Jianliang-Shen/Ragtime_Panthera/1_3D_Model/0_Solidworks2022/有d435/gripper/夹爪外壳.SLDPRT

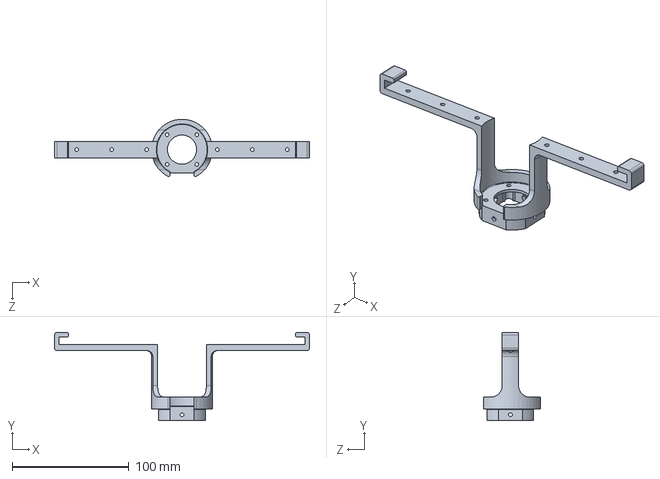
[picture p18: CAD file, 2025-05-28]
1_3D_Model/0_Solidworks2022/有d435/gripper/夹爪外壳.SLDPRT
218.6 x 75.5 x 49.3 mm
