Jianliang-Shen/Ragtime_Panthera/1_3D_Model/0_Solidworks2022/有d435/gripper/平行夹爪stl/外壳内挡块.STL

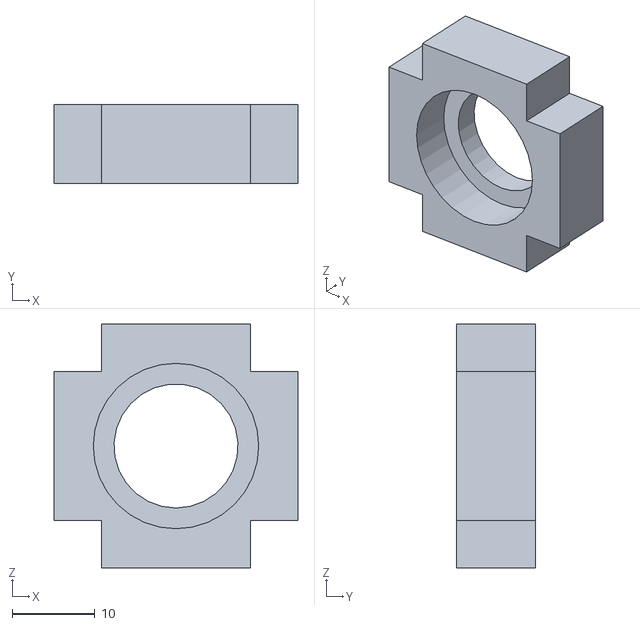
[picture p19: CAD file, 2025-05-28]
1_3D_Model/0_Solidworks2022/有d435/gripper/平行夹爪stl/外壳内挡块.STL
29.5 x 9.50 x 29.5
