Jianliang-Shen/Ragtime_Panthera/1_3D_Model/2_JLC_metalplate/304_stanless_steel/三四轴连杆.STEP

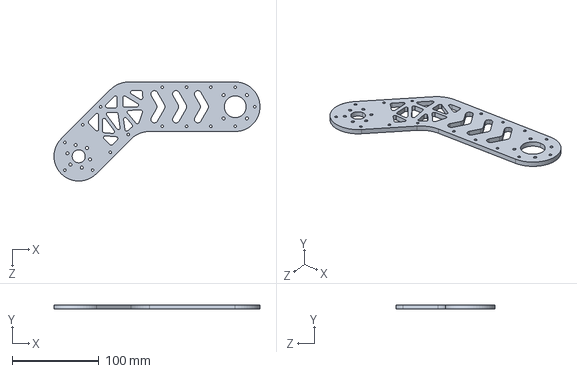
[picture p20: CAD file, 2025-06-30]
1_3D_Model/2_JLC_metalplate/304_stanless_steel/三四轴连杆.STEP
236.9 x 5.00 x 113.9 mm
