Jianliang-Shen/Ragtime_Panthera/1_3D_Model/2_JLC_metalplate/6061_aluminum_alloy/五六轴连接件1.STEP

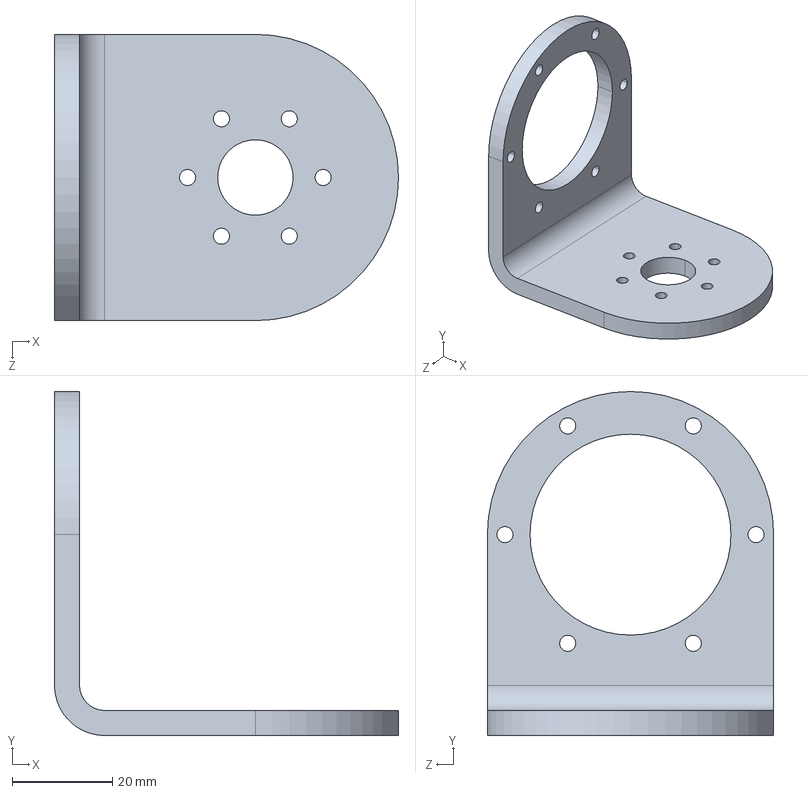
[picture p21: CAD file, 2025-05-02]
1_3D_Model/2_JLC_metalplate/6061_aluminum_alloy/五六轴连接件1.STEP
68.5 x 68.5 x 57.0 mm
