Jianliang-Shen/Ragtime_Panthera/6_Panthera_Robot/assets/link1.STL

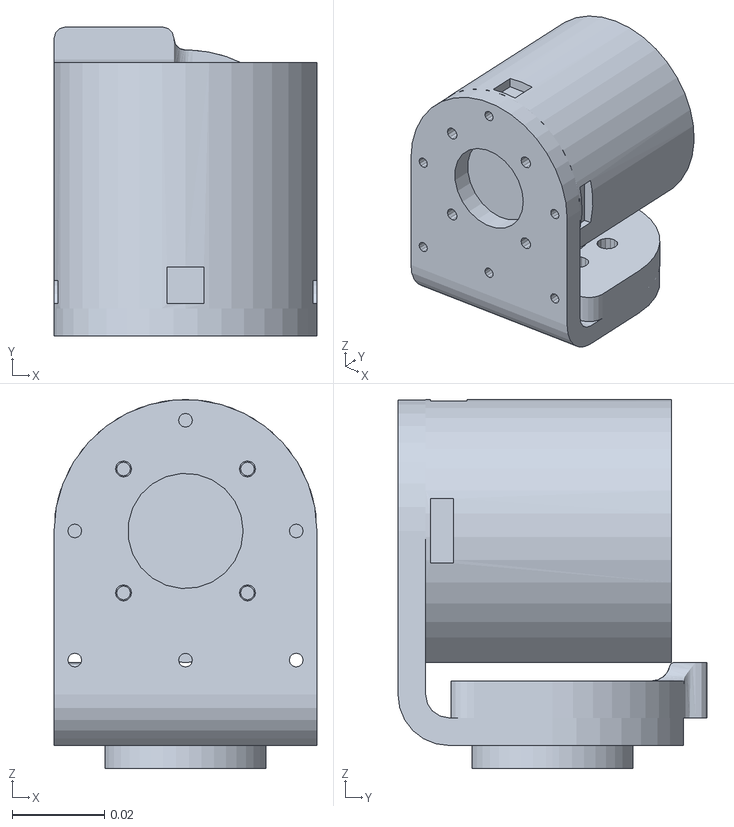
[picture p22: CAD file, 2025-05-02]
6_Panthera_Robot/assets/link1.STL
0.057 x 0.067 x 0.08
