Jianliang-Shen/Ragtime_Panthera/6_Panthera_Robot/assets/table/tabletop.obj

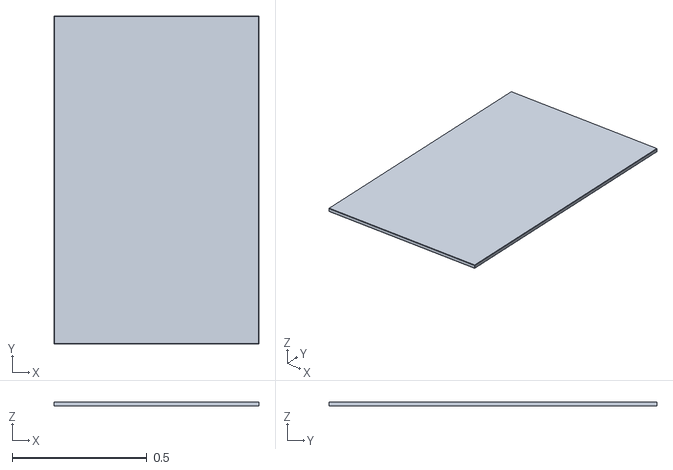
[picture p23: CAD file, 2025-08-23]
6_Panthera_Robot/assets/table/tabletop.obj
0.762 x 1.22 x 0.016
