Jianliang-Shen/Ragtime_Panthera/1_3D_Model/0_Solidworks2022/无d435/arm/四五轴连接件.SLDPRT

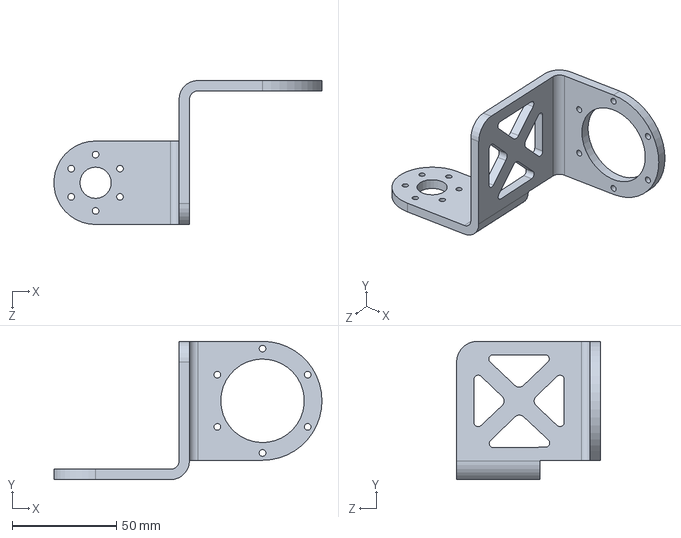
[picture p24: CAD file, 2025-06-30]
1_3D_Model/0_Solidworks2022/无d435/arm/四五轴连接件.SLDPRT
128.4 x 66.3 x 69.0 mm
