Jianliang-Shen/Ragtime_Panthera/1_3D_Model/0_Solidworks2022/无d435/gripper/MGW9导轨滑块模组/MGW9C滑块.SLDPRT

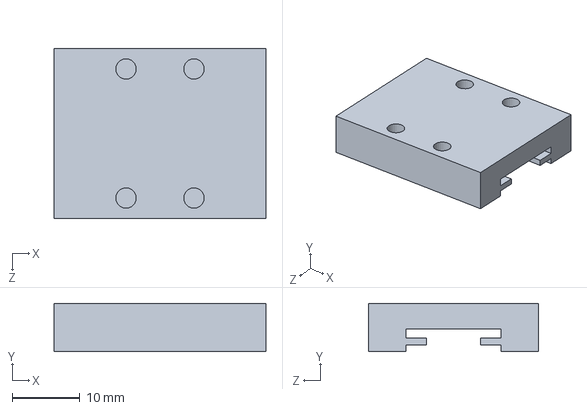
[picture p25: CAD file, 2025-05-02]
1_3D_Model/0_Solidworks2022/无d435/gripper/MGW9导轨滑块模组/MGW9C滑块.SLDPRT
31.2 x 7.10 x 25.0 mm
