Jianliang-Shen/Ragtime_Panthera/1_3D_Model/0_Solidworks2022/无d435/gripper/齿条.SLDPRT

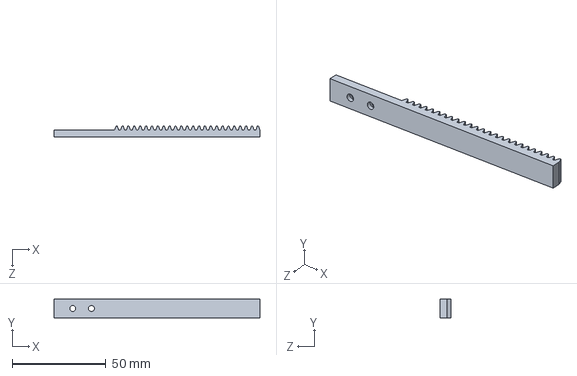
[picture p26: CAD file, 2025-05-28]
1_3D_Model/0_Solidworks2022/无d435/gripper/齿条.SLDPRT
110.0 x 10.0 x 6.00 mm
