Jianliang-Shen/Ragtime_Panthera/1_3D_Model/0_Solidworks2022/有d435/gripper/MGW9导轨滑块模组/MGW9导轨.SLDPRT

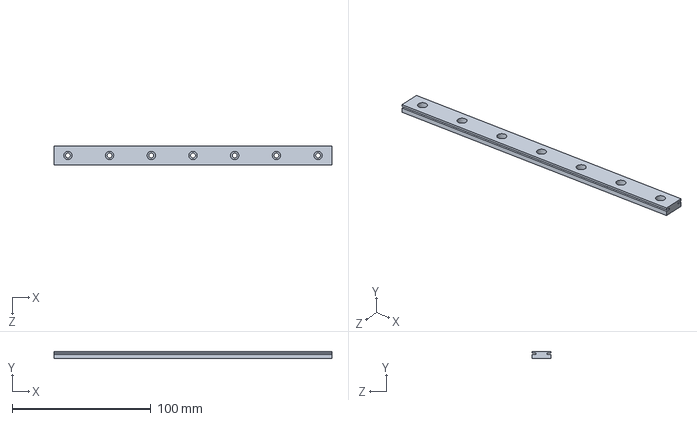
[picture p27: CAD file, 2025-05-02]
1_3D_Model/0_Solidworks2022/有d435/gripper/MGW9导轨滑块模组/MGW9导轨.SLDPRT
200.0 x 5.20 x 14.0 mm
