Jianliang-Shen/Ragtime_Panthera/1_3D_Model/2_JLC_metalplate/304_stanless_steel/二三轴连杆.STEP

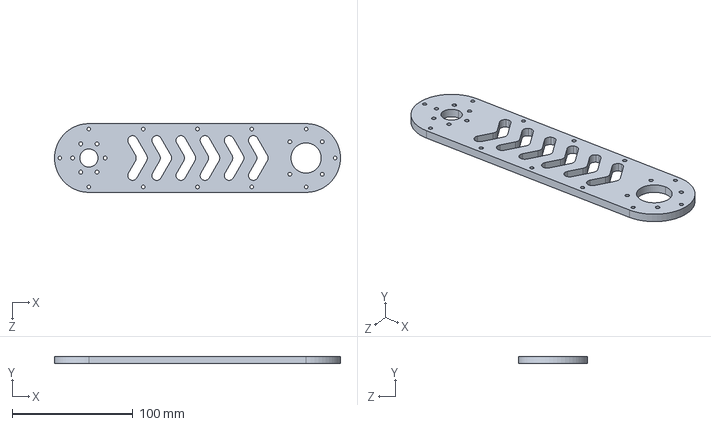
[picture p28: CAD file, 2025-06-30]
1_3D_Model/2_JLC_metalplate/304_stanless_steel/二三轴连杆.STEP
237.0 x 6.00 x 57.0 mm
