Jianliang-Shen/Ragtime_Panthera/6_Panthera_Robot/assets/link6.STL

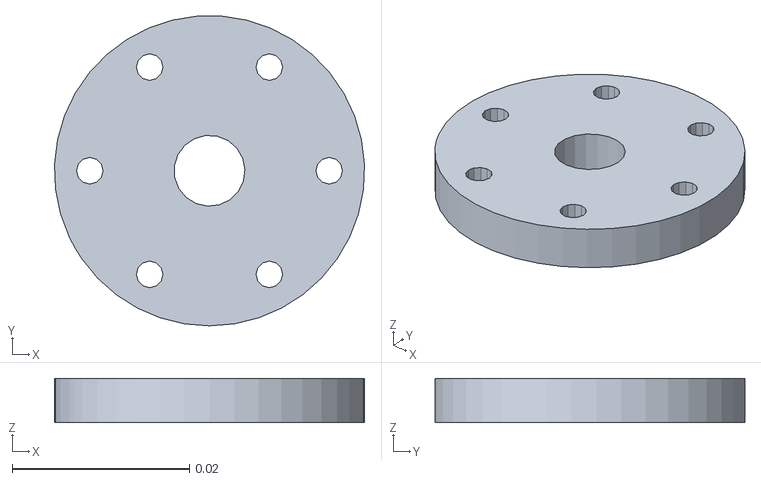
[picture p29: CAD file, 2025-05-02]
6_Panthera_Robot/assets/link6.STL
0.035 x 0.0349 x 0.005
