Jianliang-Shen/Ragtime_Panthera/6_Panthera_Robot/assets/table/tablelegs.obj

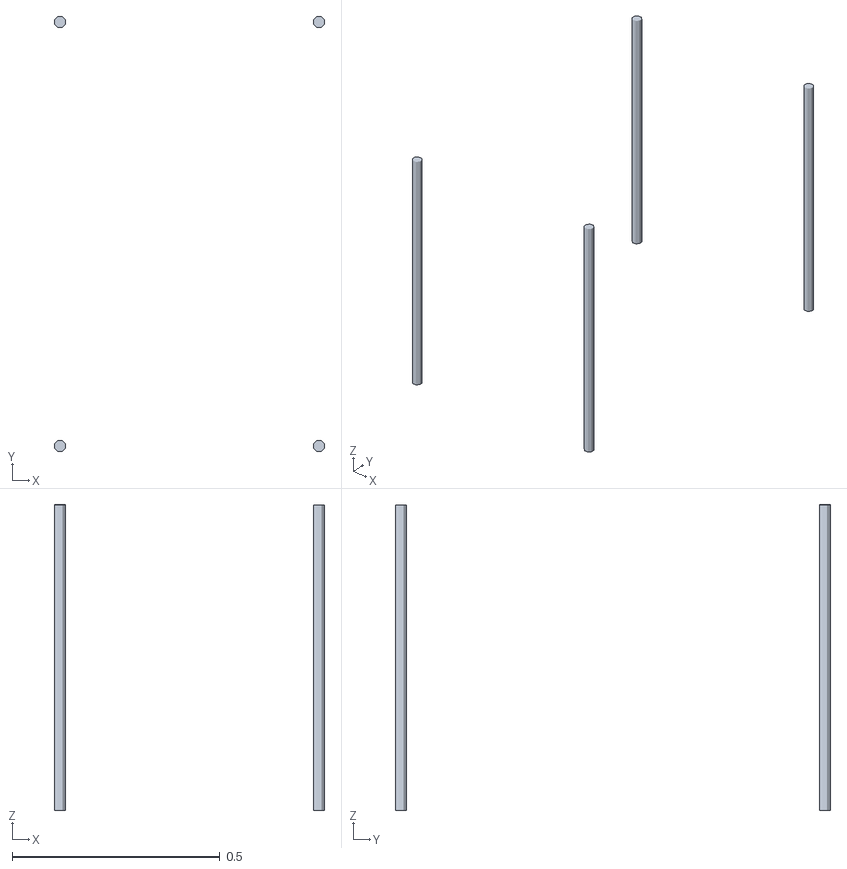
[picture p30: CAD file, 2025-08-23]
6_Panthera_Robot/assets/table/tablelegs.obj
0.65 x 1.05 x 0.737
