Jianliang-Shen/Ragtime_Panthera/1_3D_Model/0_Solidworks2022/无d435/arm/4310电机/4310电机定子.SLDPRT

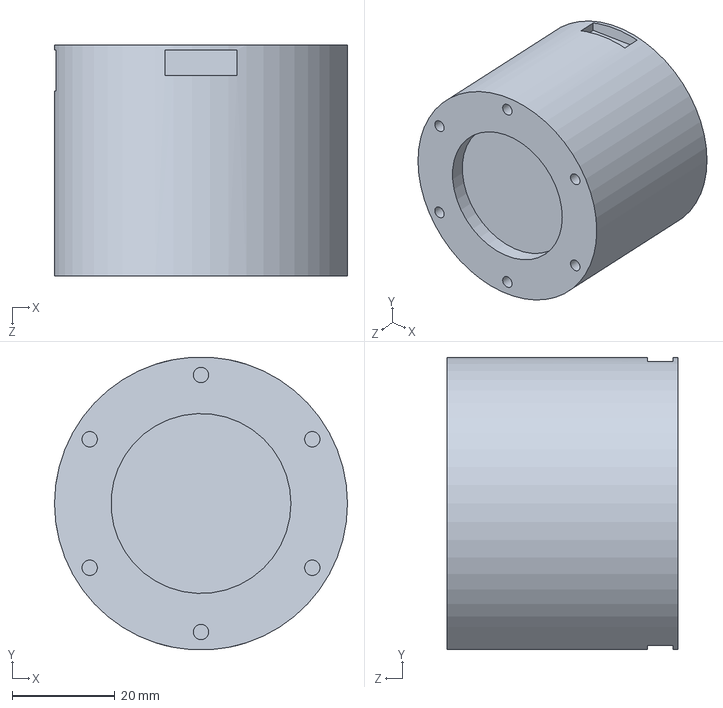
[picture p31: CAD file, 2025-05-02]
1_3D_Model/0_Solidworks2022/无d435/arm/4310电机/4310电机定子.SLDPRT
57.0 x 56.9 x 45.0 mm
