Jianliang-Shen/Ragtime_Panthera/1_3D_Model/0_Solidworks2022/无d435/arm/底板.SLDPRT

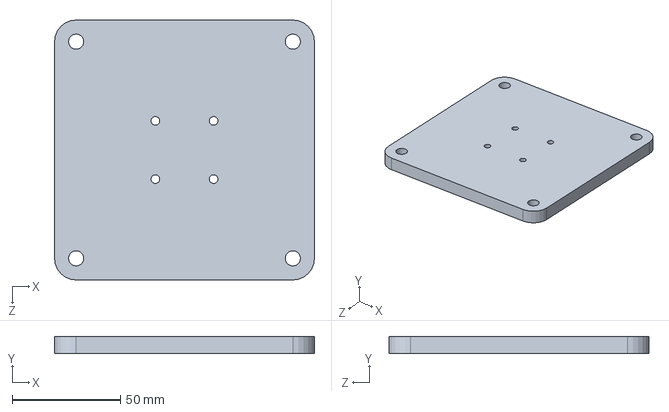
[picture p32: CAD file, 2025-05-28]
1_3D_Model/0_Solidworks2022/无d435/arm/底板.SLDPRT
120.0 x 8.00 x 120.0 mm
