Jianliang-Shen/Ragtime_Panthera/1_3D_Model/0_Solidworks2022/无d435/gripper/达妙3510轮毂电机/3510定子.SLDPRT

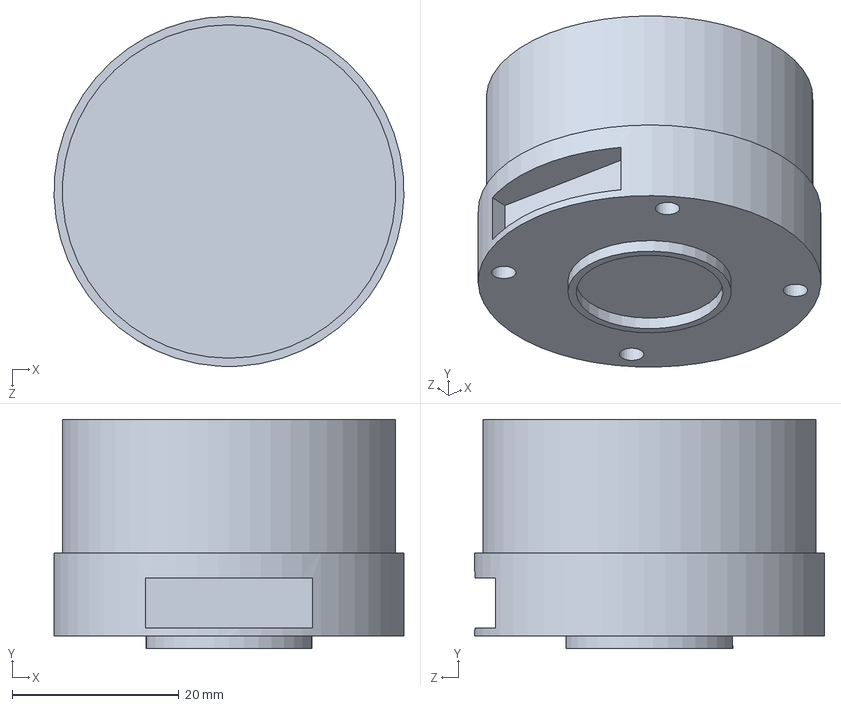
[picture p33: CAD file, 2025-05-02]
1_3D_Model/0_Solidworks2022/无d435/gripper/达妙3510轮毂电机/3510定子.SLDPRT
42.0 x 27.5 x 42.0 mm
