Jianliang-Shen/Ragtime_Panthera/1_3D_Model/2_JLC_metalplate/304_stanless_steel/一二轴连接件.STEP

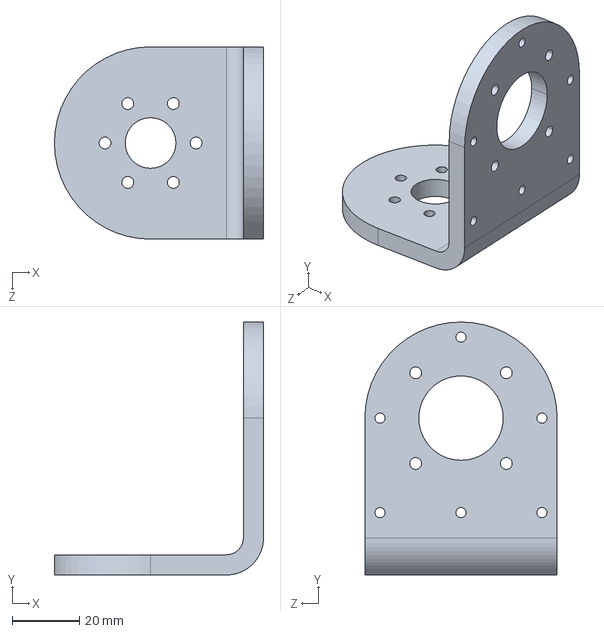
[picture p34: CAD file, 2025-05-02]
1_3D_Model/2_JLC_metalplate/304_stanless_steel/一二轴连接件.STEP
62.0 x 75.0 x 57.0 mm
