Jianliang-Shen/Ragtime_Panthera/6_Panthera_Robot/assets/link4.STL

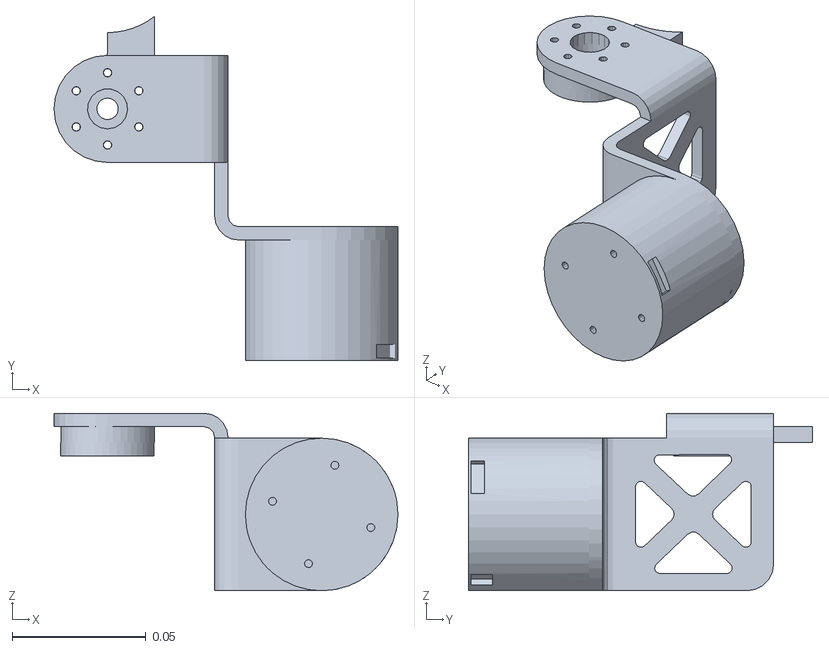
[picture p35: CAD file, 2025-05-02]
6_Panthera_Robot/assets/link4.STL
0.129 x 0.129 x 0.0663
