Jianliang-Shen/Ragtime_Panthera/6_Panthera_Robot/assets/table/Desk.obj

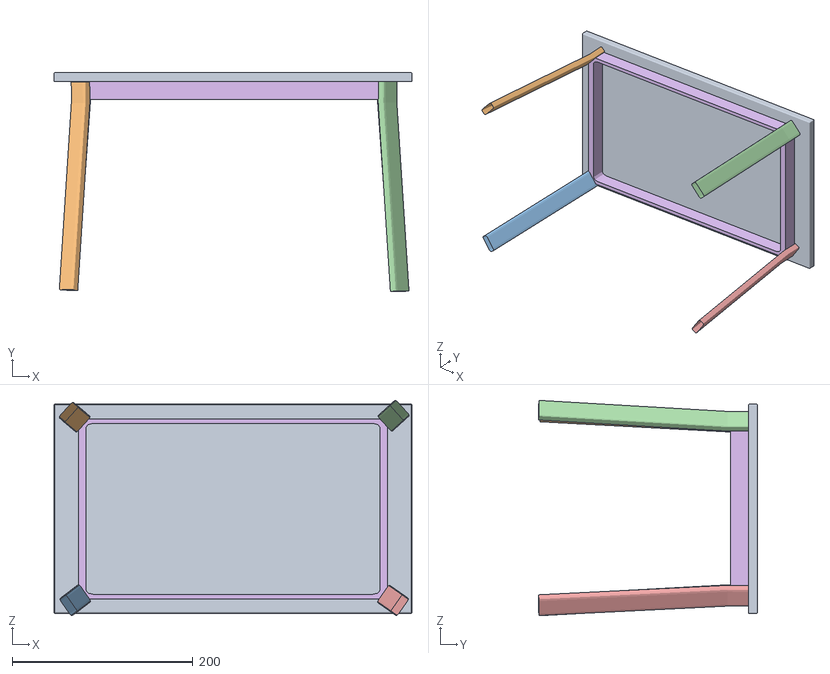
[picture p36: CAD file, 2025-08-23]
6_Panthera_Robot/assets/table/Desk.obj
396.0 x 242.2 x 238.1
Top
Leg:4
Leg:3
Leg:2
Leg:1
Under
