Jianliang-Shen/Ragtime_Panthera/1_3D_Model/0_Solidworks2022/无d435/gripper/转子齿轮连接件.SLDPRT

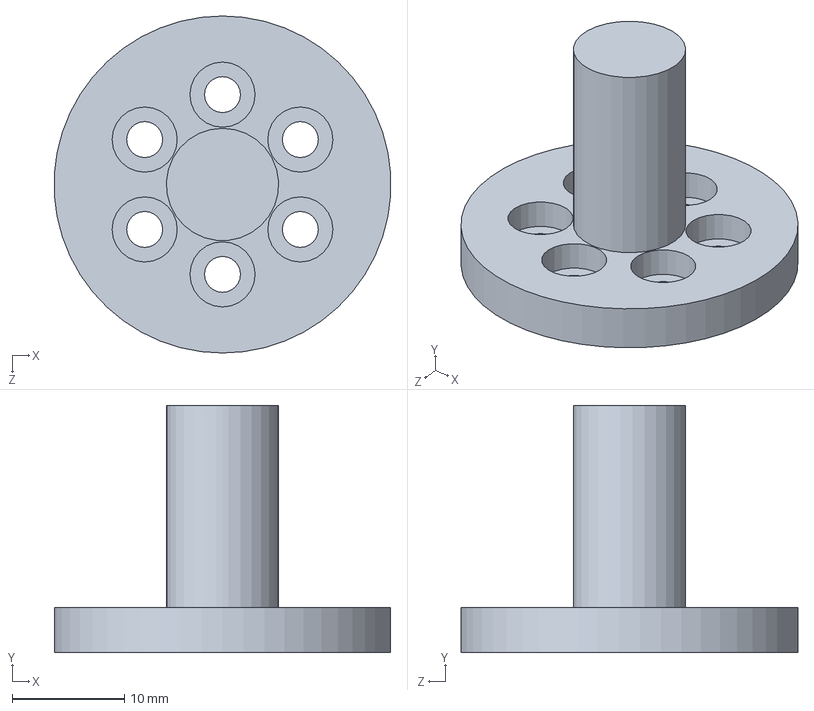
[picture p37: CAD file, 2025-05-28]
1_3D_Model/0_Solidworks2022/无d435/gripper/转子齿轮连接件.SLDPRT
29.9 x 22.0 x 30.0 mm
