Jianliang-Shen/Ragtime_Panthera/1_3D_Model/0_Solidworks2022/有d435/arm/二三轴连杆定位件.SLDPRT

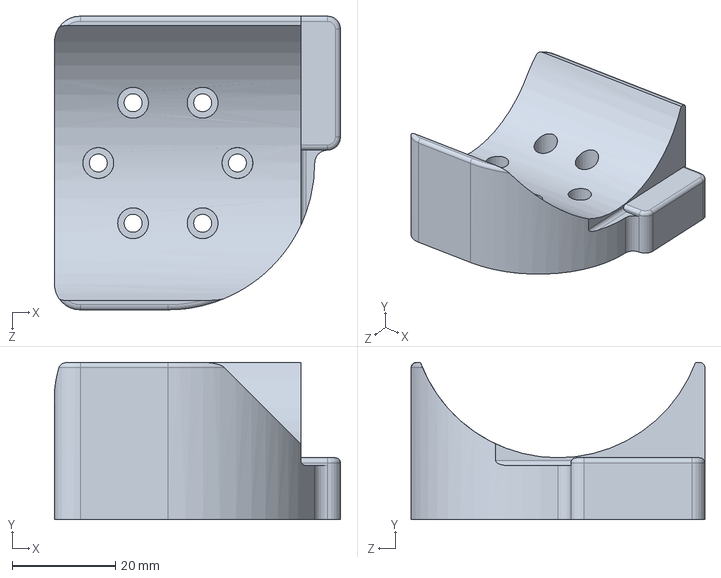
[picture p38: CAD file, 2025-05-28]
1_3D_Model/0_Solidworks2022/有d435/arm/二三轴连杆定位件.SLDPRT
55.5 x 30.5 x 57.0 mm
