Jianliang-Shen/Ragtime_Panthera/6_Panthera_Robot/assets/gripper_2_link.STL

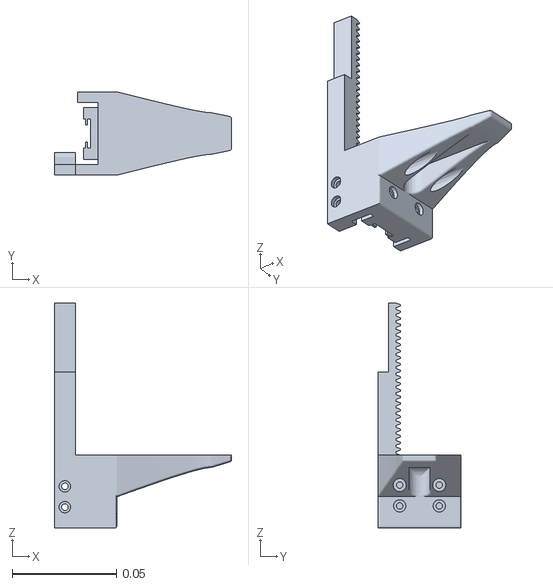
[picture p39: CAD file, 2025-05-02]
6_Panthera_Robot/assets/gripper_2_link.STL
0.085 x 0.04 x 0.108
