Jianliang-Shen/Ragtime_Panthera/1_3D_Model/0_Solidworks2022/无d435/gripper/平行夹爪stl/手指.STL

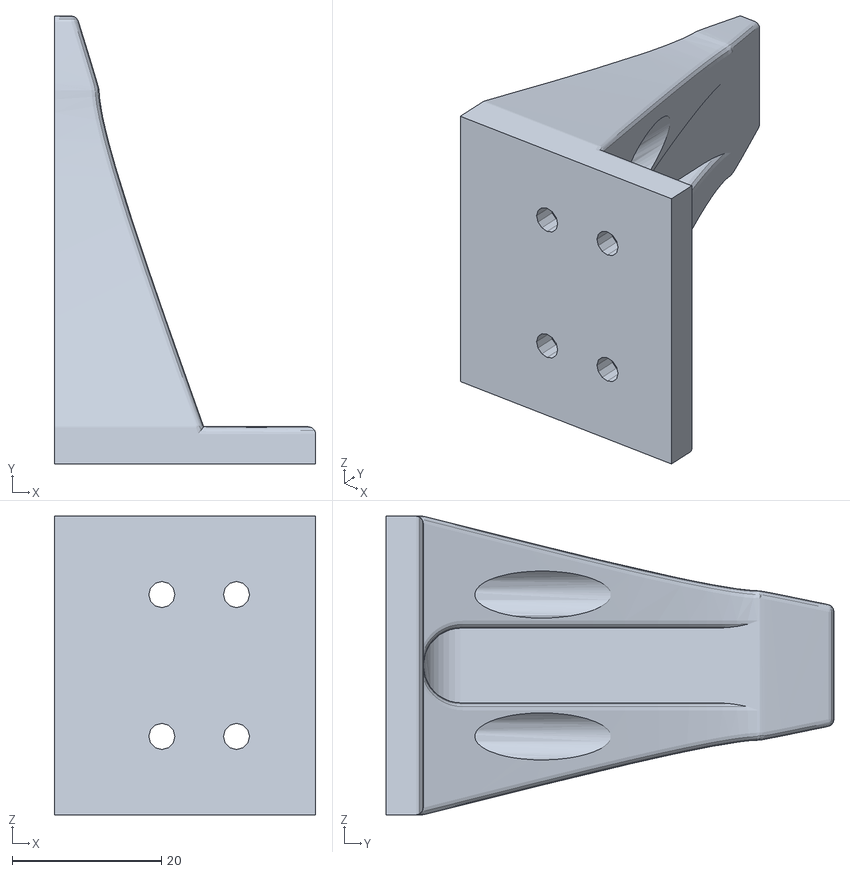
[picture p40: CAD file, 2025-05-02]
1_3D_Model/0_Solidworks2022/无d435/gripper/平行夹爪stl/手指.STL
35.0 x 60.0 x 40.0
