Jianliang-Shen/Ragtime_Panthera/6_Panthera_Robot/assets/link3.STL

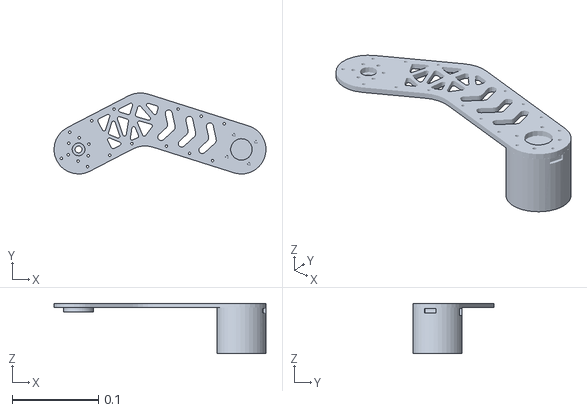
[picture p41: CAD file, 2025-05-02]
6_Panthera_Robot/assets/link3.STL
0.246 x 0.0939 x 0.0583
