Jianliang-Shen/Ragtime_Panthera/1_3D_Model/0_Solidworks2022/无d435/arm/四五轴连杆定位件.SLDPRT

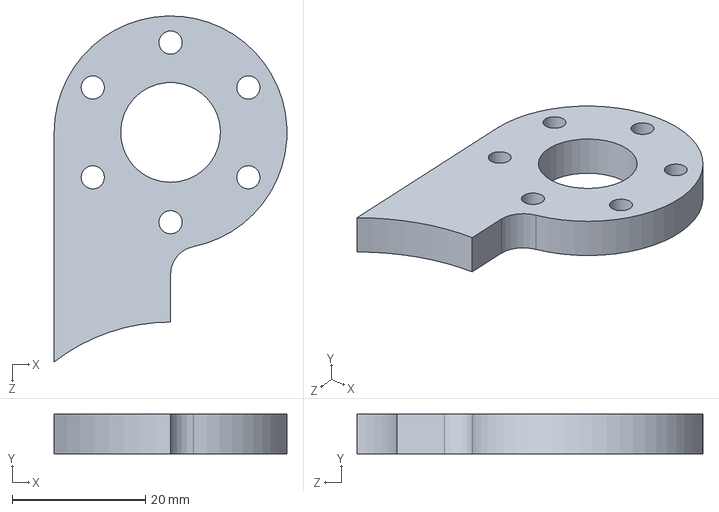
[picture p42: CAD file, 2025-05-02]
1_3D_Model/0_Solidworks2022/无d435/arm/四五轴连杆定位件.SLDPRT
35.0 x 6.00 x 52.0 mm
