Jianliang-Shen/Ragtime_Panthera/1_3D_Model/0_Solidworks2022/有d435/arm/法兰(带d435).SLDPRT

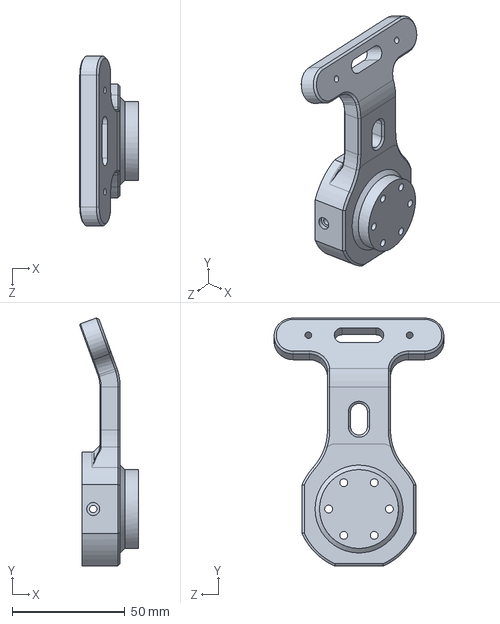
[picture p43: CAD file, 2025-05-28]
1_3D_Model/0_Solidworks2022/有d435/arm/法兰(带d435).SLDPRT
26.0 x 110.1 x 75.5 mm
