Jianliang-Shen/Ragtime_Panthera/1_3D_Model/0_Solidworks2022/无d435/gripper/外壳内挡块.SLDPRT

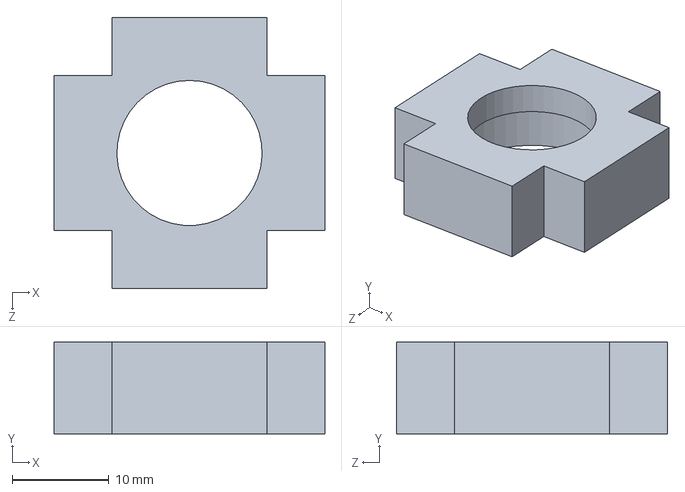
[picture p44: CAD file, 2025-05-28]
1_3D_Model/0_Solidworks2022/无d435/gripper/外壳内挡块.SLDPRT
28.0 x 9.50 x 28.0 mm
