Jianliang-Shen/Ragtime_Panthera/1_3D_Model/0_Solidworks2022/无d435/gripper/平行夹爪stl/末端法兰.STL

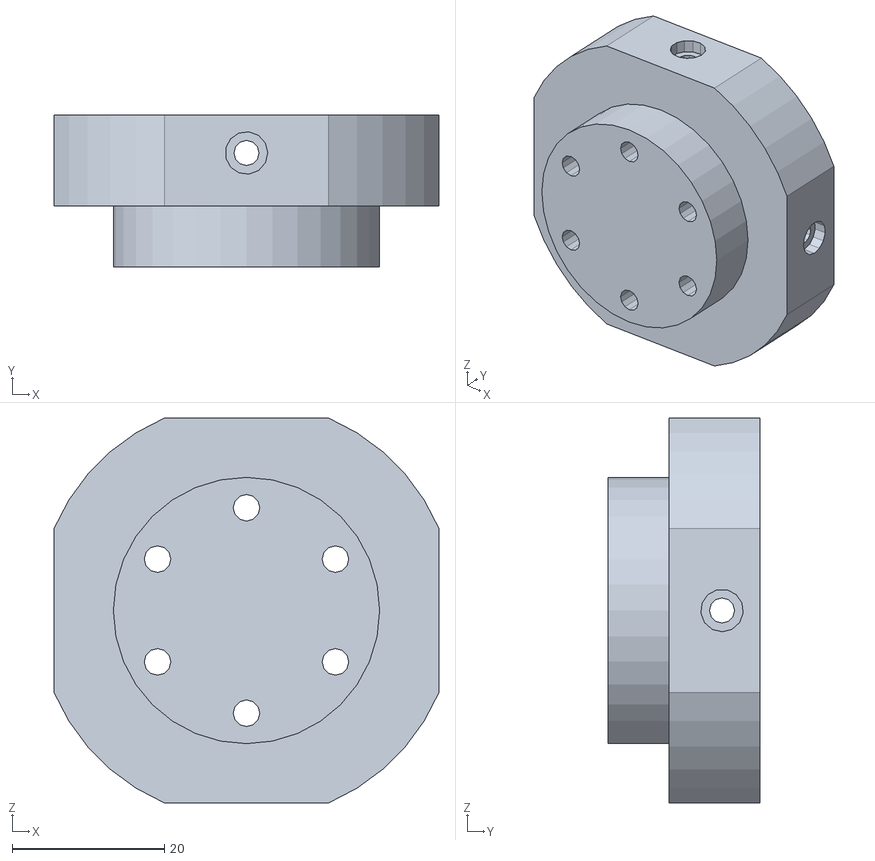
[picture p45: CAD file, 2025-05-02]
1_3D_Model/0_Solidworks2022/无d435/gripper/平行夹爪stl/末端法兰.STL
50.6 x 20.0 x 50.6
