Jianliang-Shen/Ragtime_Panthera/1_3D_Model/0_Solidworks2022/有d435/arm/IntelRealsense_D435_Multibody.SLDPRT

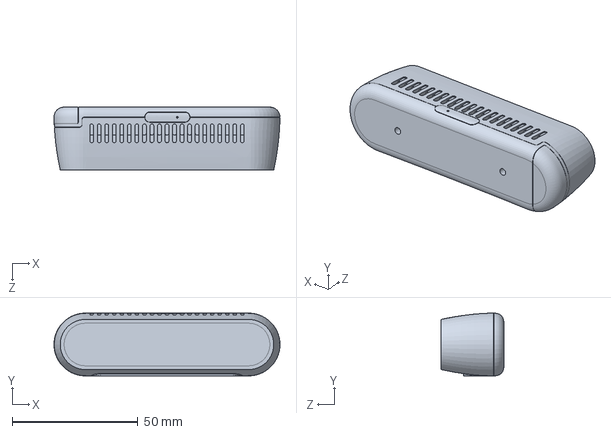
[picture p46: CAD file, 2025-05-28]
1_3D_Model/0_Solidworks2022/有d435/arm/IntelRealsense_D435_Multibody.SLDPRT
90.0 x 25.0 x 25.0 mm
