Jianliang-Shen/Ragtime_Panthera/6_Panthera_Robot/assets/link5.STL

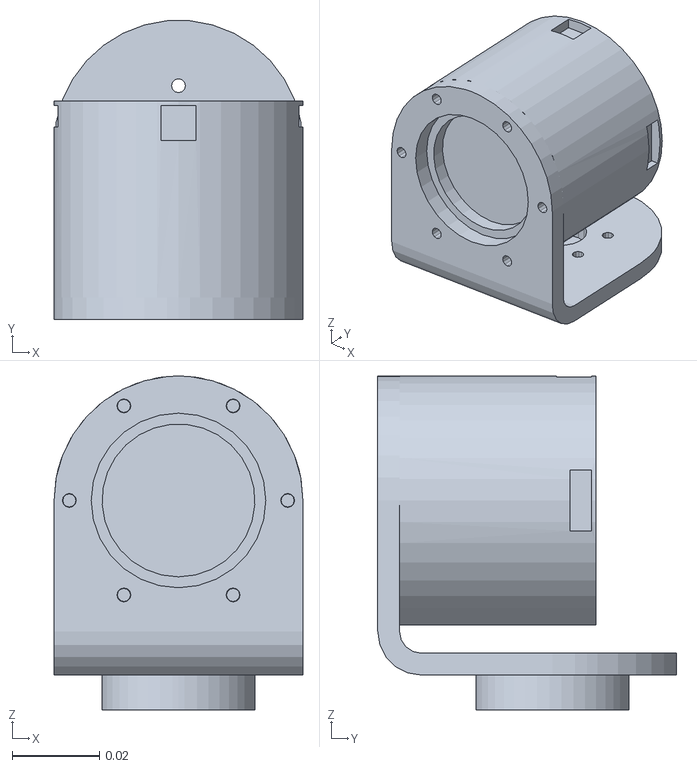
[picture p47: CAD file, 2025-05-02]
6_Panthera_Robot/assets/link5.STL
0.057 x 0.0684 x 0.0765
