Jianliang-Shen/Ragtime_Panthera/1_3D_Model/0_Solidworks2022/有d435/arm/圆头末端.SLDPRT

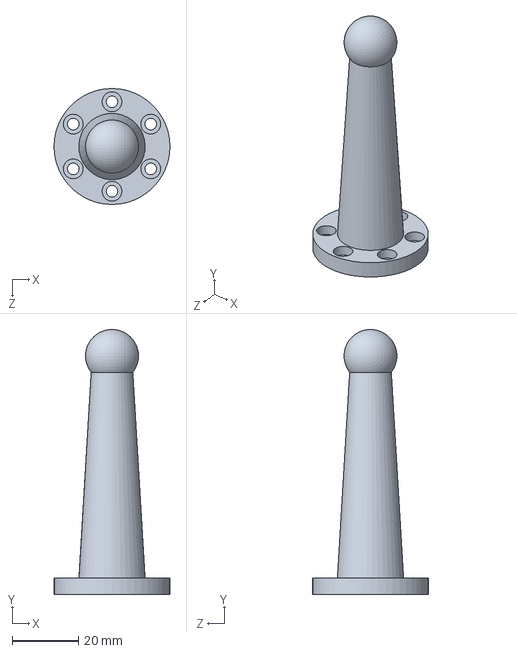
[picture p48: CAD file, 2025-05-02]
1_3D_Model/0_Solidworks2022/有d435/arm/圆头末端.SLDPRT
35.0 x 80.0 x 35.0 mm
