Jianliang-Shen/Ragtime_Panthera/6_Panthera_Robot/assets/base_link.STL

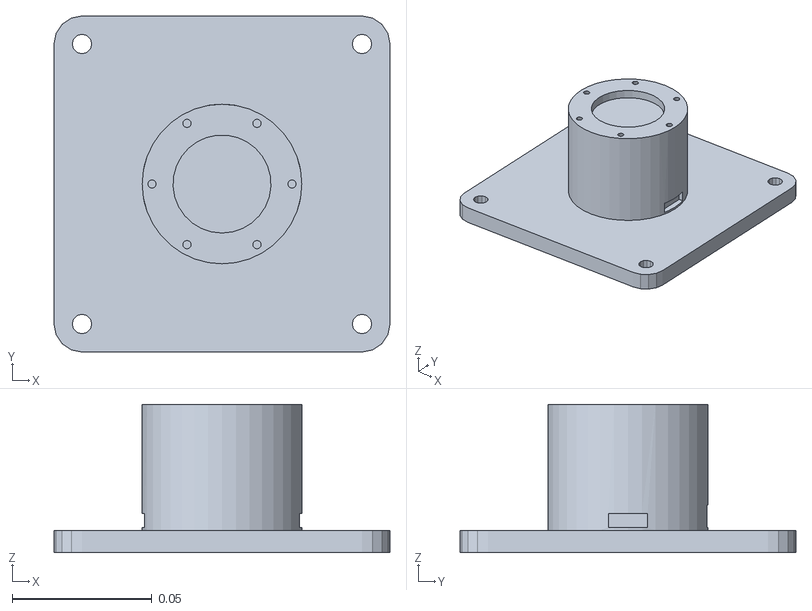
[picture p49: CAD file, 2025-05-02]
6_Panthera_Robot/assets/base_link.STL
0.12 x 0.12 x 0.053
