Jianliang-Shen/Ragtime_Panthera/1_3D_Model/0_Solidworks2022/有d435/arm/五六轴垫块.SLDPRT

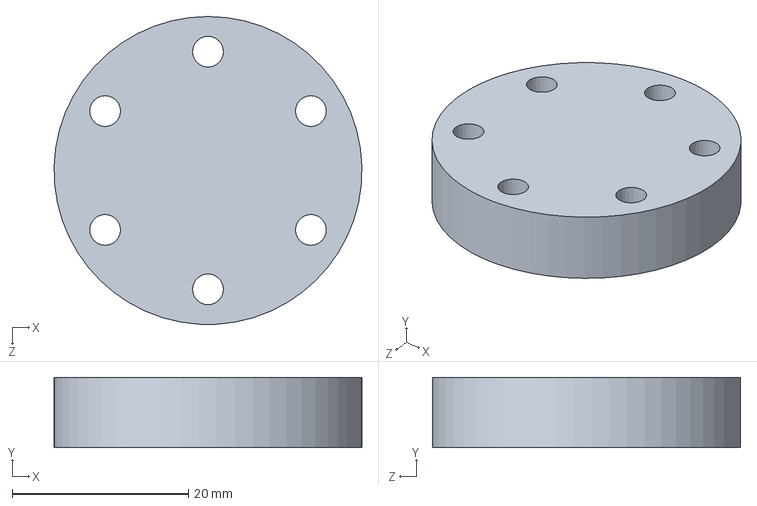
[picture p50: CAD file, 2025-05-02]
1_3D_Model/0_Solidworks2022/有d435/arm/五六轴垫块.SLDPRT
35.0 x 8.00 x 35.0 mm
