Jianliang-Shen/Ragtime_Panthera/6_Panthera_Robot/assets/link2.STL

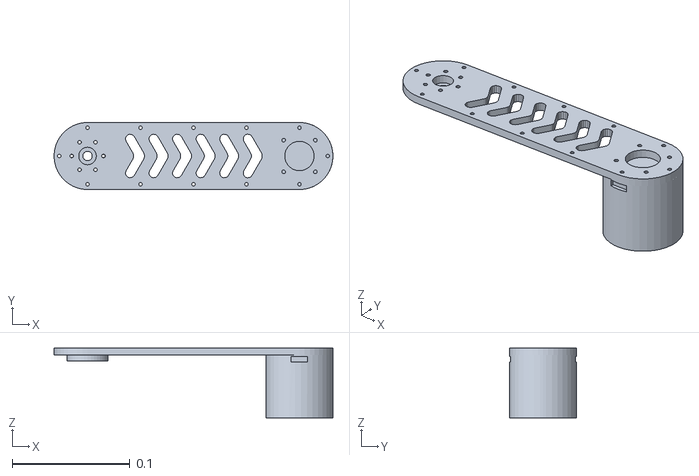
[picture p51: CAD file, 2025-05-02]
6_Panthera_Robot/assets/link2.STL
0.237 x 0.057 x 0.0593
