Jianliang-Shen/Ragtime_Panthera/1_3D_Model/0_Solidworks2022/无d435/arm/从动轴.SLDPRT

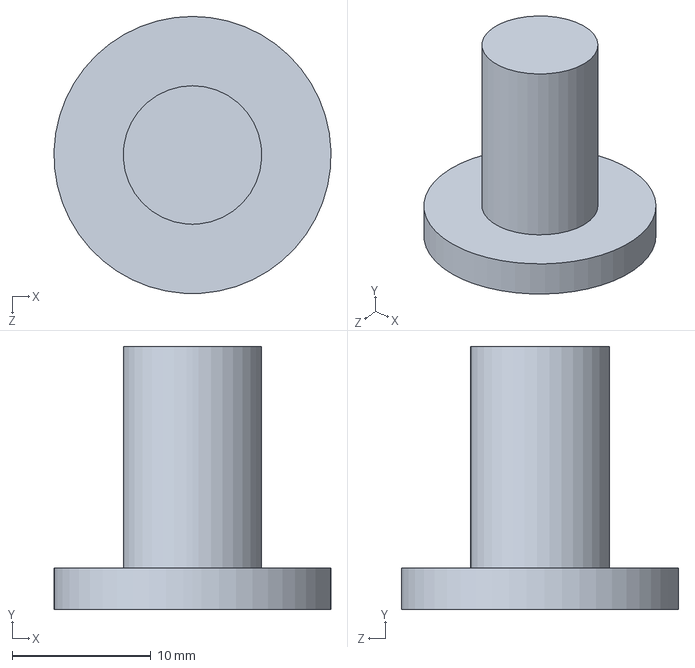
[picture p52: CAD file, 2025-05-02]
1_3D_Model/0_Solidworks2022/无d435/arm/从动轴.SLDPRT
20.0 x 19.0 x 20.0 mm
