Jianliang-Shen/Ragtime_Panthera/1_3D_Model/0_Solidworks2022/无d435/gripper/rack spur rectangular_gb.SLDPRT

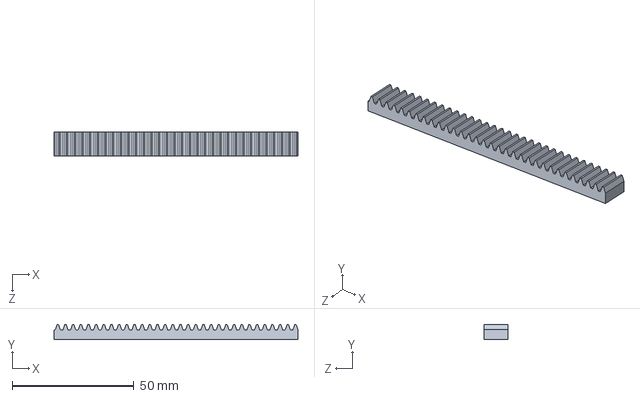
[picture p53: CAD file, 2025-05-02]
1_3D_Model/0_Solidworks2022/无d435/gripper/rack spur rectangular_gb.SLDPRT
100.0 x 6.00 x 10.0 mm
