Jianliang-Shen/Ragtime_Panthera/1_3D_Model/0_Solidworks2022/有d435/gripper/手指齿条.SLDPRT

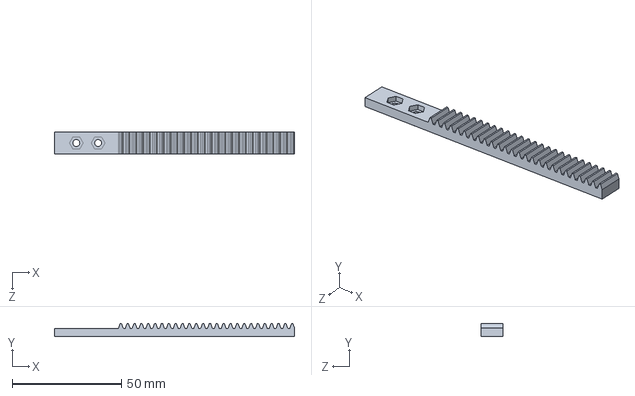
[picture p54: CAD file, 2025-05-02]
1_3D_Model/0_Solidworks2022/有d435/gripper/手指齿条.SLDPRT
110.0 x 6.00 x 10.0 mm
