Jianliang-Shen/Ragtime_Panthera/6_Panthera_Robot/assets/gripper_centor_link.STL

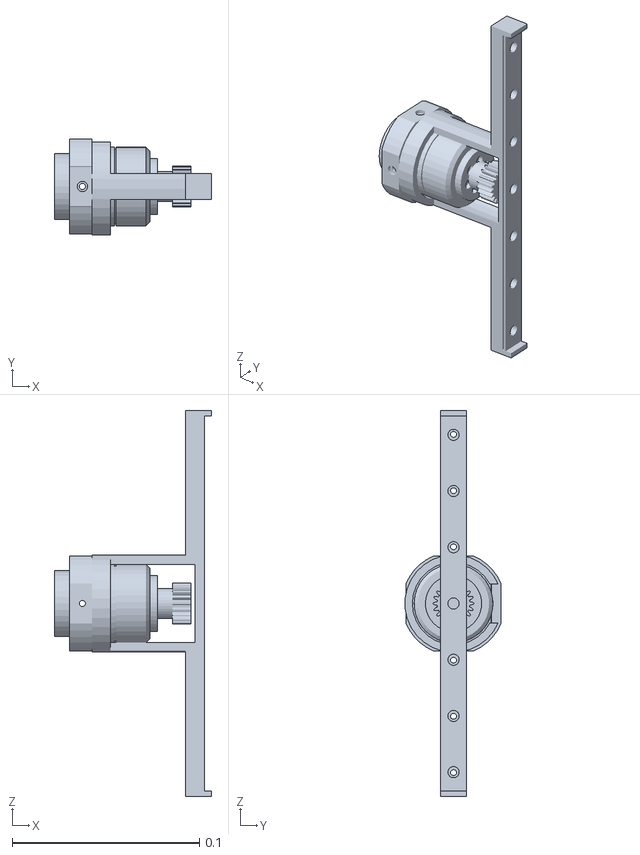
[picture p55: CAD file, 2025-05-02]
6_Panthera_Robot/assets/gripper_centor_link.STL
0.084 x 0.0512 x 0.206
