Jianliang-Shen/Ragtime_Panthera/1_3D_Model/0_Solidworks2022/无d435/gripper/手指齿条零件.SLDPRT

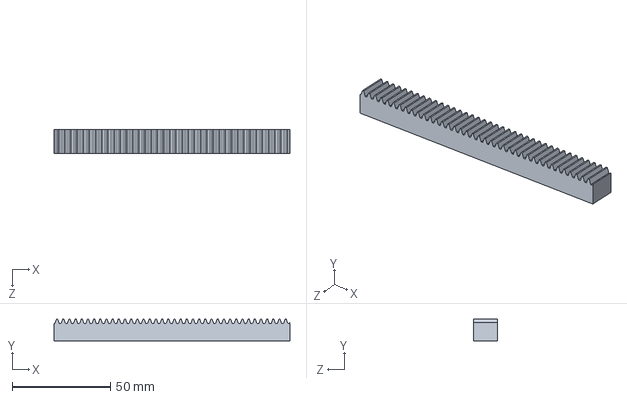
[picture p56: CAD file, 2025-05-02]
1_3D_Model/0_Solidworks2022/无d435/gripper/手指齿条零件.SLDPRT
120.0 x 11.0 x 12.0 mm
