Jianliang-Shen/Ragtime_Panthera/1_3D_Model/0_Solidworks2022/有d435/gripper/1模20齿凸台齿轮.SLDPRT

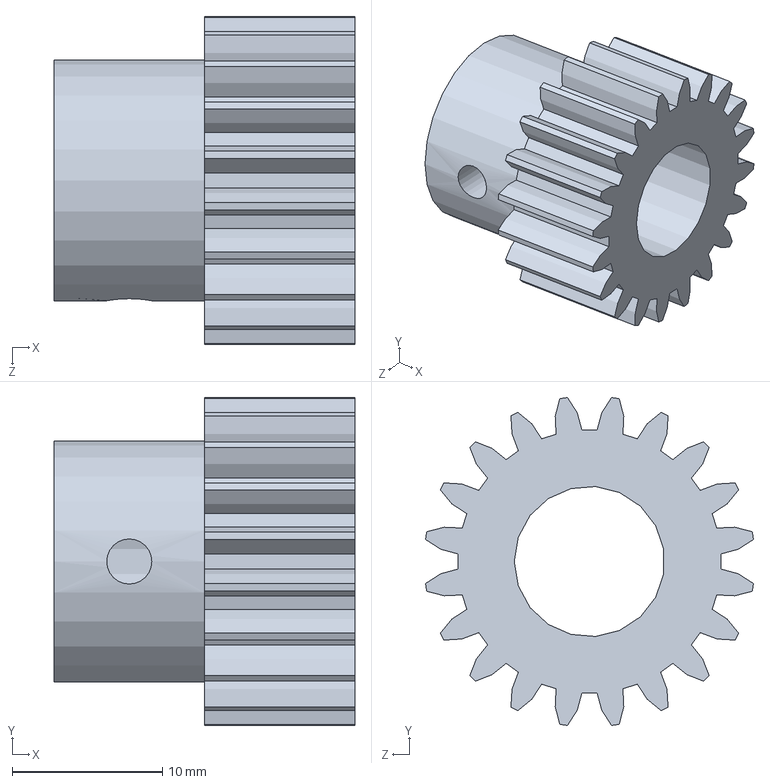
[picture p57: CAD file, 2025-05-02]
1_3D_Model/0_Solidworks2022/有d435/gripper/1模20齿凸台齿轮.SLDPRT
20.0 x 21.8 x 21.8 mm
