Jianliang-Shen/Ragtime_Panthera/1_3D_Model/0_Solidworks2022/有d435/gripper/GB - Spur gear 1M 20T 20PA 10FW ---S20B16H18L10.0N.SLDPRT

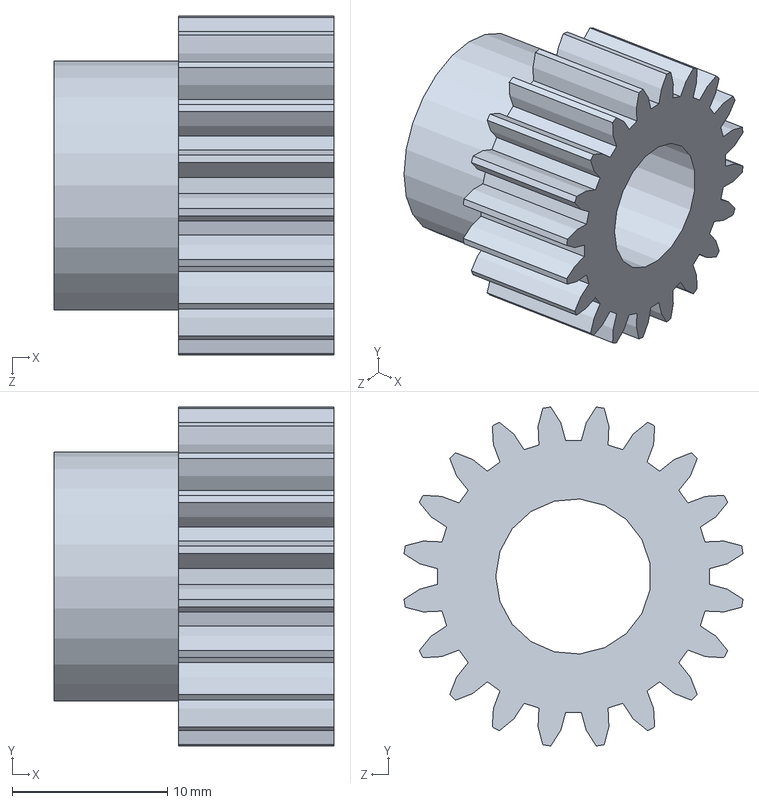
[picture p58: CAD file, 2025-05-02]
1_3D_Model/0_Solidworks2022/有d435/gripper/GB - Spur gear 1M 20T 20PA 10FW ---S20B16H18L10.0N.SLDPRT
18.0 x 21.8 x 21.8 mm
